Man-fred/esp_schaltbare_Steckdose/zcommon.h

#ifndef COMMON_H
#define COMMON_H

// ********** Globale Einstellungen zum Layout und zur Version **************
#define IICTEST
#define USE_LED_BUILTIN
String mVersionNr = "V01-01-01.";
// ********** Ende der Einstellungen ****************************************

#include <TimeLib.h>             //<Time.h> http://www.arduino.cc/playground/Code/Time
#define DEBUG_OUTPUT Serial
#define DBG_OUTPUT_PORT Serial

#ifdef IICTEST
# ifdef USE_LED_BUILTIN
    String mVersionVariante = "iic.";
# else
    String mVersionVariante = "i2c.";
# endif
#else
  String mVersionVariante = "min.";
#endif //ifdef IIC

#ifdef ARDUINO_ESP8266_NODEMCU
  const byte board = 1;
  String mVersionBoard = "nodemcu";
#elif ARDUINO_ESP8266_WEMOS_D1MINI
  const byte board = 2;
  String mVersionBoard = "d1_mini";
#else
  const byte board = 3;
  String mVersionBoard = "unknown";
#endif

// enables OTA updates
#include <ESP8266httpUpdate.h>

#include <ESP8266WebServer.h>

ESP8266WebServer server;
#define LOGINLAENGE 32
#define COOKIE_MAX 10
#define COOKIE_ADMINISTRATOR 1
#define COOKIE_BENUTZER 2
const char * headerKeys[] = {"User-Agent","Set-Cookie","Cookie","Date","Content-Type","Connection"} ;
size_t headerKeysCount = 6;

char name_timer[LOGINLAENGE] = "Wifi 4-fach Timer";
char name_r[4][LOGINLAENGE]; 
char AdminName[LOGINLAENGE] = "admin\0";
char AdminPasswort[LOGINLAENGE] = "\0";
char UserName[LOGINLAENGE] = "user\0";
char UserPasswort[LOGINLAENGE] = "\0";
char UpdateServer[LOGINLAENGE] = "192.168.178.60\0";
char timeserver[LOGINLAENGE] = "time.nist.gov\0";
int  UserCookie[COOKIE_MAX];// = [0,0,0,0,0,0,0,0,0,0];
int  UserStatus[COOKIE_MAX];// = [0,0,0,0,0,0,0,0,0,0];
int  UserNext=0;
int  UserCurrent = -1;

boolean sommerzeit = false;
const char* serverIndex = "<form method='POST' action='/upload' enctype='multipart/form-data'><input type='file' name='upload'><input type='submit' value='Upload'></form>";

// Timer
unsigned long NTPTime = 0, RTCTime = 0, RTCSync = 0, ZeitTemp = 0, ZeitTempMin = 0, ZeitTempStd = 0, ZeitTempTag = 0;
//time_t NTPTime = 0, RTCTime = 0, RTCSync = 0, ZeitTemp = 0, ZeitTempMin = 0, ZeitTempStd = 0, ZeitTempTag = 0;
// Status
byte NTPok = 0, WLANok = 0, IOok = 0, RTCok = 0, DISPLAYok = 0;
boolean AP = 0; // Accesspoint Modus aus


#endif
